serisman/pdk-digital-clock/pcb-s16/output/OSHPARK - Bottom.png

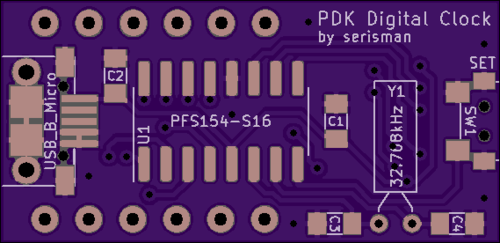
pcb-s16/output/OSHPARK - Bottom.png
