serisman/pdk-digital-clock/pcb-s16/output/OSHPARK - Top.png

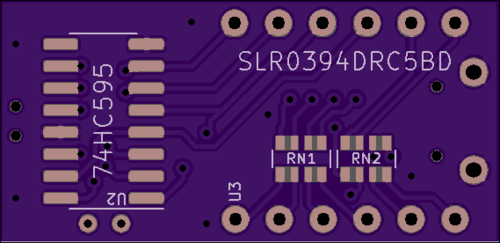
pcb-s16/output/OSHPARK - Top.png
